vuckale/takt11800/Docs/jpgs/kicad_pcb_editor.jpg

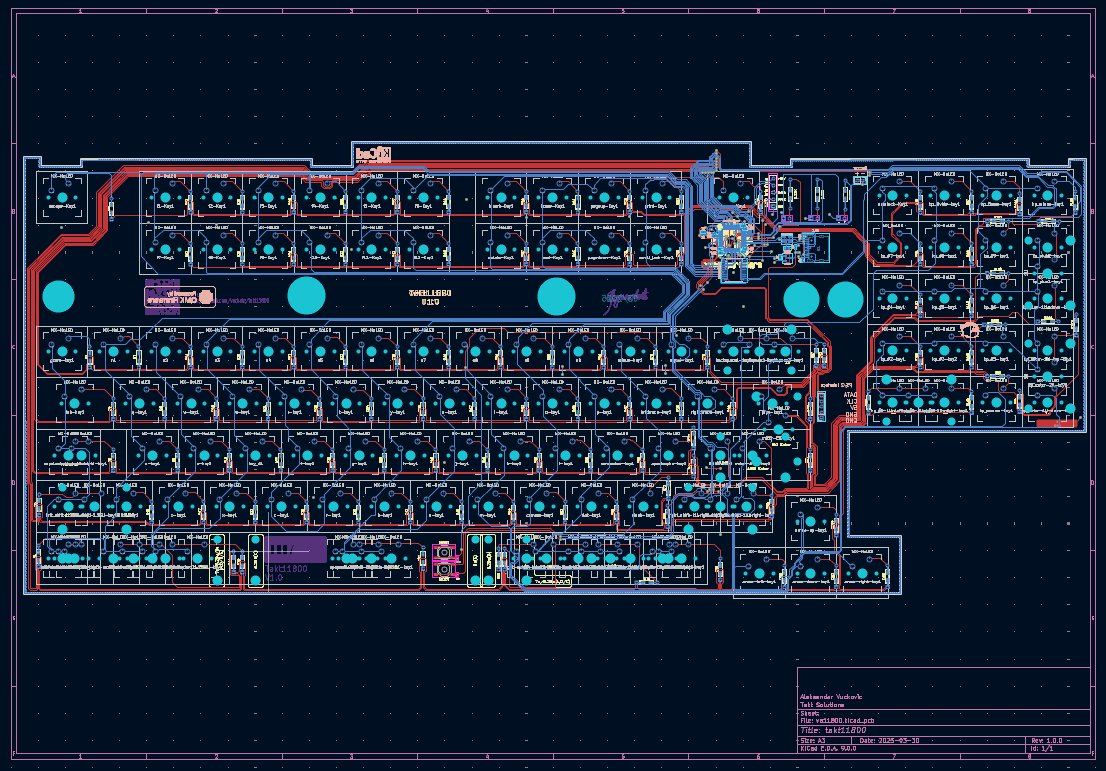
Docs/jpgs/kicad_pcb_editor.jpg
