vuckale/takt11800/Docs/pcbway/pcbway_package.JPEG

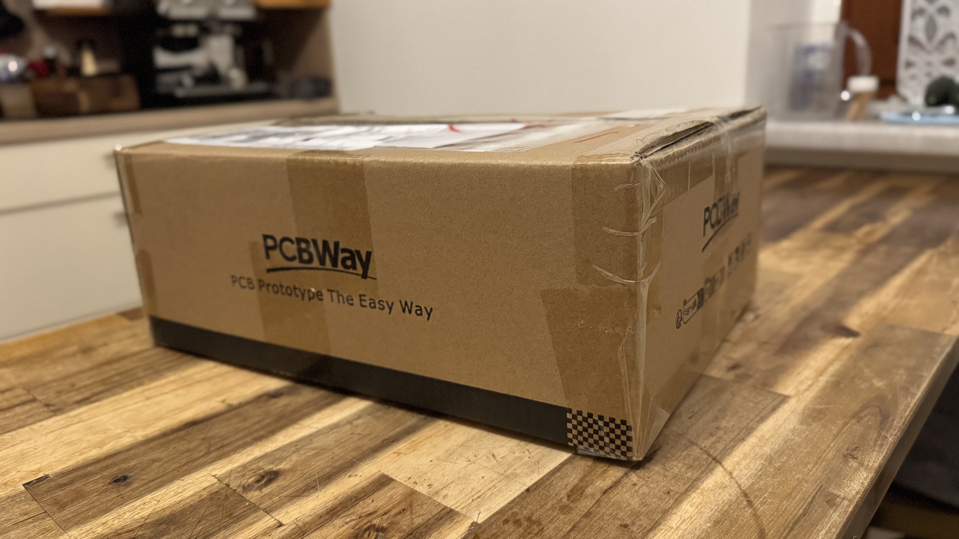
Docs/pcbway/pcbway_package.JPEG
