vuckale/takt11800/Docs/pcbway/Screenshot 2025-06-19 024208.png

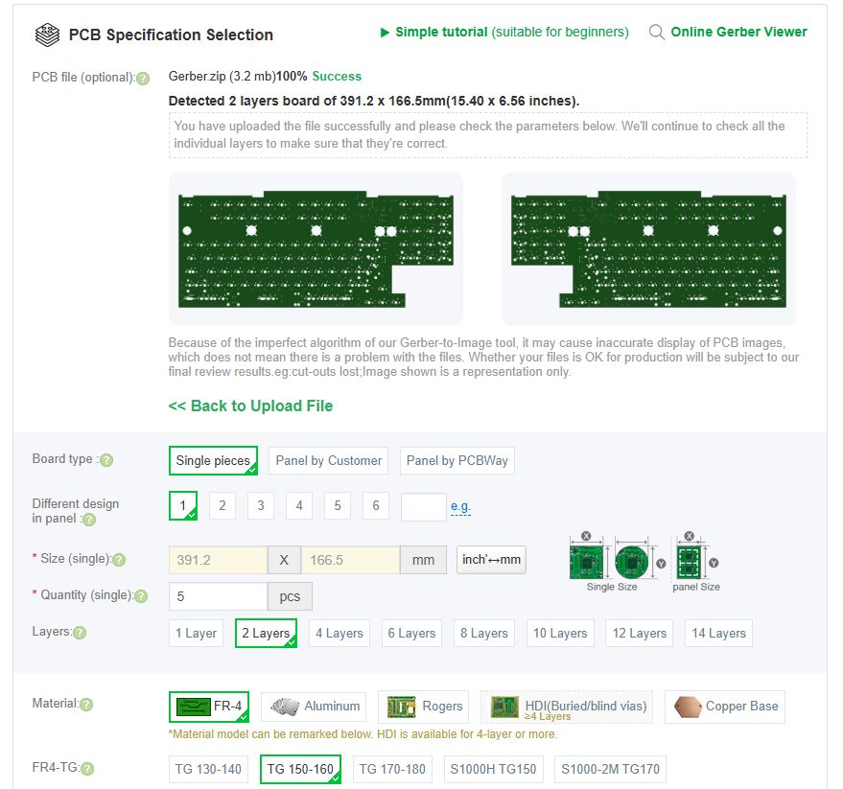
Docs/pcbway/Screenshot 2025-06-19 024208.png
