vuckale/takt11800/Docs/pngs/3d_mcu.png

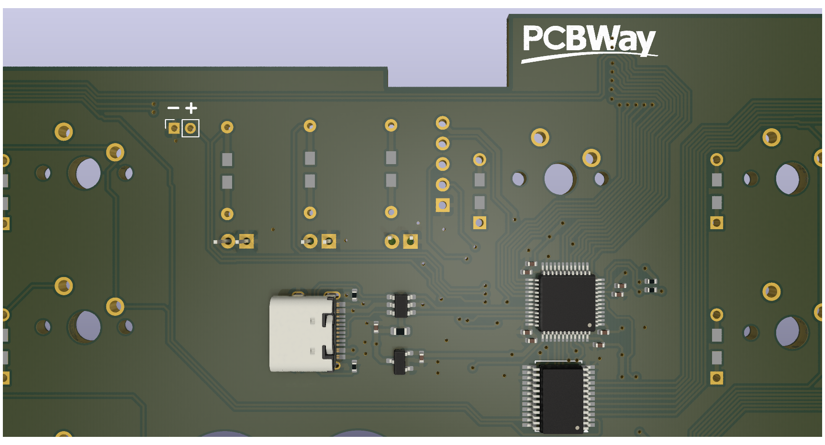
Docs/pngs/3d_mcu.png
