vuckale/takt11800/Docs/pngs/3d_pcb_front.png

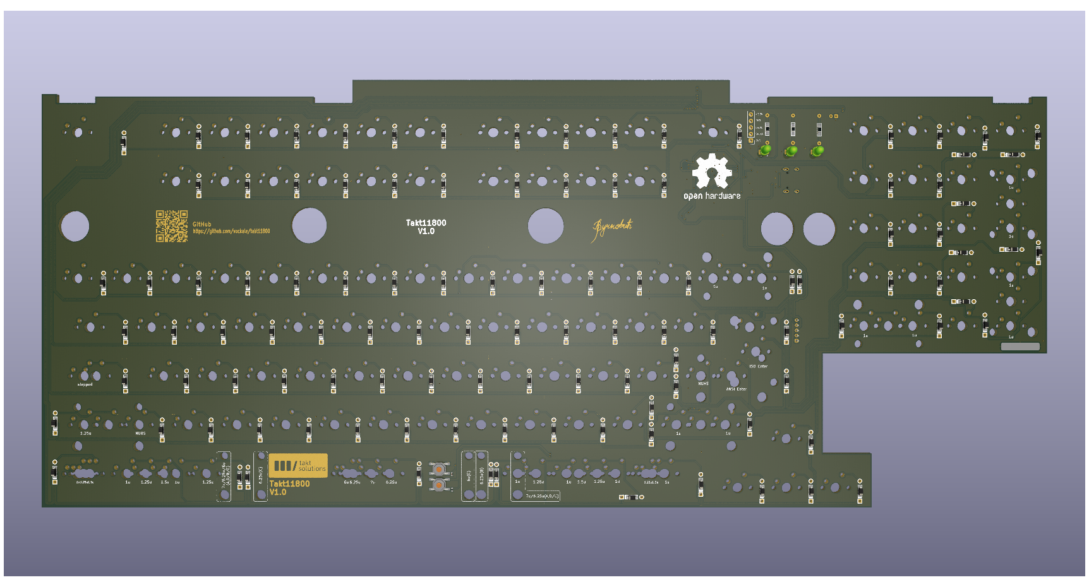
Docs/pngs/3d_pcb_front.png
